pdaehne/Atari-ST-Floppy-Adapter/images/Pins_in_Socket.jpg

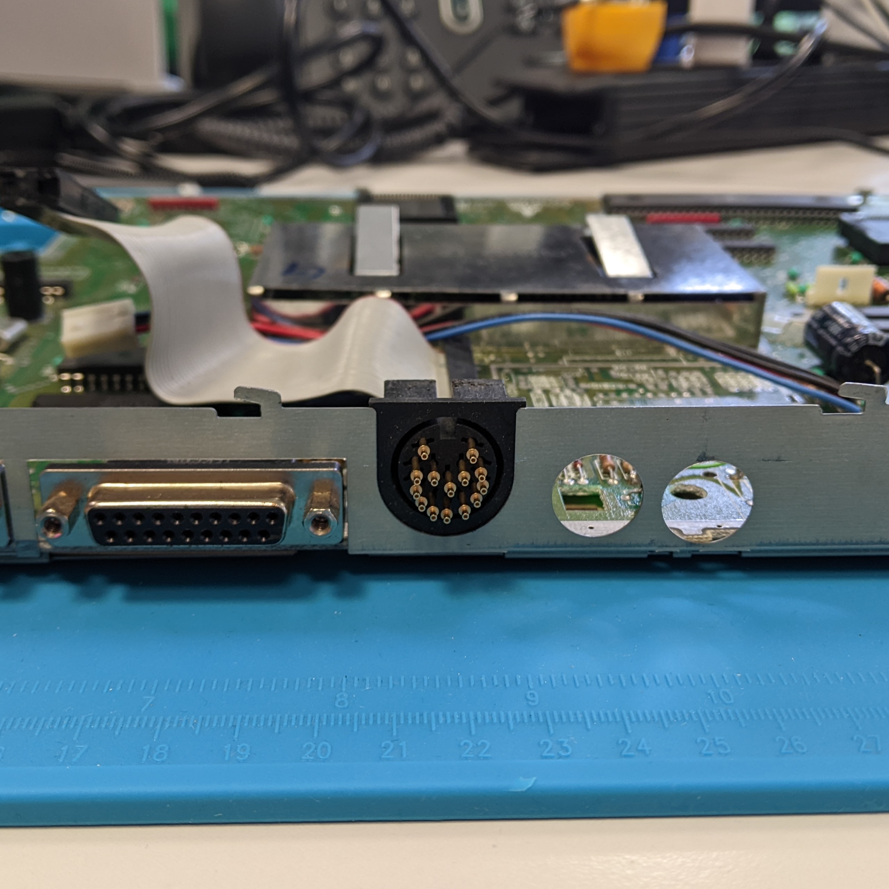
images/Pins_in_Socket.jpg
